rzeldent/meshtastic-esp32-c3-dx-lr30/meshtastic/variants/esp32c3/heltec_esp32c3/pins_arduino.h

#ifndef Pins_Arduino_h
#define Pins_Arduino_h

#include <stdint.h>

static const uint8_t SDA = 20;
static const uint8_t SCL = 21;

static const uint8_t SS = 8;
static const uint8_t MOSI = 7;
static const uint8_t MISO = 6;
static const uint8_t SCK = 9;

static const uint8_t A0 = 0;
static const uint8_t A1 = 1;
static const uint8_t A2 = 2;
static const uint8_t A3 = 3;
static const uint8_t A4 = 4;
static const uint8_t A5 = 5;

#endif /* Pins_Arduino_h */
